Marc0-dev/SJ413-clock/CarClock/src/PCF8563.c

#include "PCF8563.h"
void Write(uint8_t reg, unsigned char value){
    IIC_Init(400000, WRITE_ADDRESS);
    while( I2C_GetFlagStatus(I2C1, I2C_FLAG_BUSY) != RESET);
    I2C_GenerateSTART(I2C1, ENABLE);
    while( !I2C_CheckEvent( I2C1, I2C_EVENT_MASTER_MODE_SELECT ) );
    I2C_Send7bitAddress( I2C1, WRITE_ADDRESS, I2C_Direction_Transmitter );
    while (!I2C_CheckEvent(I2C1, I2C_EVENT_MASTER_TRANSMITTER_MODE_SELECTED));
    while (I2C_GetFlagStatus(I2C1, I2C_FLAG_TXE) == RESET);
    I2C_SendData(I2C1, reg);
    while (!I2C_CheckEvent(I2C1, I2C_EVENT_MASTER_BYTE_TRANSMITTED));
    I2C_SendData(I2C1, value);
    while (!I2C_CheckEvent(I2C1, I2C_EVENT_MASTER_BYTE_TRANSMITTED));
    I2C_GenerateSTOP(I2C1, ENABLE);
}
unsigned char Read(uint8_t reg){
    IIC_Init(400000, READ_ADDRESS);
    while( I2C_GetFlagStatus(I2C1, I2C_FLAG_BUSY) != RESET);
    I2C_GenerateSTART(I2C1, ENABLE);
    while( !I2C_CheckEvent( I2C1, I2C_EVENT_MASTER_MODE_SELECT ) );
    I2C_Send7bitAddress( I2C1, READ_ADDRESS, I2C_Direction_Transmitter );
    while (!I2C_CheckEvent(I2C1, I2C_EVENT_MASTER_TRANSMITTER_MODE_SELECTED));
    while (I2C_GetFlagStatus(I2C1, I2C_FLAG_TXE) == RESET);
    I2C_SendData(I2C1, reg);
    while (!I2C_CheckEvent(I2C1, I2C_EVENT_MASTER_BYTE_TRANSMITTED));
    I2C_GenerateSTOP(I2C1, ENABLE);
    IIC_Init(400000, READ_ADDRESS);
    while( I2C_GetFlagStatus(I2C1, I2C_FLAG_BUSY) != RESET);
    I2C_GenerateSTART(I2C1, ENABLE);
    while( !I2C_CheckEvent( I2C1, I2C_EVENT_MASTER_MODE_SELECT ) );
    I2C_Send7bitAddress( I2C1, READ_ADDRESS, I2C_Direction_Receiver );
    while (!I2C_CheckEvent(I2C1, I2C_EVENT_MASTER_RECEIVER_MODE_SELECTED));
    unsigned char data = I2C_ReceiveData(I2C1);
    while (!I2C_CheckEvent(I2C1, I2C_EVENT_MASTER_BYTE_RECEIVED));
    I2C_GenerateSTOP(I2C1, ENABLE);
    return data;
}
void QueryTime(unsigned char  * min, unsigned char * hour){
    IIC_Init(400000, READ_ADDRESS);
    while( I2C_GetFlagStatus(I2C1, I2C_FLAG_BUSY) != RESET);
    I2C_GenerateSTART(I2C1, ENABLE);
    while( !I2C_CheckEvent( I2C1, I2C_EVENT_MASTER_MODE_SELECT ) );
    I2C_Send7bitAddress( I2C1, READ_ADDRESS, I2C_Direction_Transmitter );
    while (!I2C_CheckEvent(I2C1, I2C_EVENT_MASTER_TRANSMITTER_MODE_SELECTED));
    while (I2C_GetFlagStatus(I2C1, I2C_FLAG_TXE) == RESET);
    I2C_SendData(I2C1, 0x02);
    while (!I2C_CheckEvent(I2C1, I2C_EVENT_MASTER_BYTE_TRANSMITTED));
    I2C_GenerateSTOP(I2C1, ENABLE);
    IIC_Init(400000, READ_ADDRESS);
    while( I2C_GetFlagStatus(I2C1, I2C_FLAG_BUSY) != RESET);
    I2C_GenerateSTART(I2C1, ENABLE);
    while( !I2C_CheckEvent( I2C1, I2C_EVENT_MASTER_MODE_SELECT ) );
    I2C_Send7bitAddress( I2C1, READ_ADDRESS, I2C_Direction_Receiver );
    while (!I2C_CheckEvent(I2C1, I2C_EVENT_MASTER_RECEIVER_MODE_SELECTED));
    while (I2C_GetFlagStatus(I2C1, I2C_FLAG_RXNE) == RESET);
    I2C_ReceiveData(I2C1);
    while (!I2C_CheckEvent(I2C1, I2C_EVENT_MASTER_BYTE_RECEIVED));
    *min = I2C_ReceiveData(I2C1);
    while (!I2C_CheckEvent(I2C1, I2C_EVENT_MASTER_BYTE_RECEIVED));
    *hour = I2C_ReceiveData(I2C1);
    while (!I2C_CheckEvent(I2C1, I2C_EVENT_MASTER_BYTE_RECEIVED));
    I2C_GenerateSTOP(I2C1, ENABLE);
}
void WriteTime(unsigned char * min, unsigned char * hour){
    IIC_Init(400000, WRITE_ADDRESS);
    while( I2C_GetFlagStatus(I2C1, I2C_FLAG_BUSY) != RESET);
    I2C_GenerateSTART(I2C1, ENABLE);
    while( !I2C_CheckEvent( I2C1, I2C_EVENT_MASTER_MODE_SELECT ) );
    I2C_Send7bitAddress( I2C1, WRITE_ADDRESS, I2C_Direction_Transmitter );
    while (!I2C_CheckEvent(I2C1, I2C_EVENT_MASTER_TRANSMITTER_MODE_SELECTED));
    while (I2C_GetFlagStatus(I2C1, I2C_FLAG_TXE) == RESET);
    I2C_SendData(I2C1, 0x02);
    while (!I2C_CheckEvent(I2C1, I2C_EVENT_MASTER_BYTE_TRANSMITTED));
    I2C_SendData(I2C1, 0x00);
    while (!I2C_CheckEvent(I2C1, I2C_EVENT_MASTER_BYTE_TRANSMITTED));
    I2C_SendData(I2C1, *min);
    while (!I2C_CheckEvent(I2C1, I2C_EVENT_MASTER_BYTE_TRANSMITTED));
    I2C_SendData(I2C1, *hour);
    I2C_GenerateSTOP(I2C1, ENABLE);
}
