Marc0-dev/SJ413-clock/CarClock/src/BoardInit.c

#include "BoardInit.h"
void init(){
    NVIC_PriorityGroupConfig(NVIC_PriorityGroup_1);
    SystemCoreClockUpdate();
    Delay_Init();
    USART_Printf_Init(115200);
}
void initPin(uint8_t pinNumber, char bank, uint8_t mode, uint8_t speed){
    GPIO_InitTypeDef GPIO_InitStructure = {0};
    GPIO_InitStructure.GPIO_Pin = pinNumber;
    GPIO_InitStructure.GPIO_Mode = mode;
    GPIO_InitStructure.GPIO_Speed = speed;
    if(bank == 'A'){
        RCC_APB2PeriphClockCmd(RCC_APB2Periph_GPIOA, ENABLE);
        GPIO_Init(GPIOA, &GPIO_InitStructure);
    }
    else if(bank == 'C'){
        RCC_APB2PeriphClockCmd(RCC_APB2Periph_GPIOC, ENABLE);
        GPIO_Init(GPIOC, &GPIO_InitStructure);
    }
    else if(bank == 'D'){
        RCC_APB2PeriphClockCmd(RCC_APB2Periph_GPIOD, ENABLE);
        GPIO_Init(GPIOD, &GPIO_InitStructure);
    }
}
void IIC_Init(u32 speed, u16 address){
    I2C_InitTypeDef I2C_InitStructure = {0};
    GPIO_InitTypeDef GPIO_InitStructure={0};
    RCC_APB2PeriphClockCmd(RCC_APB2Periph_GPIOC | RCC_APB2Periph_AFIO, ENABLE);
    RCC_APB1PeriphClockCmd(RCC_APB1Periph_I2C1, ENABLE);
    GPIO_InitStructure.GPIO_Pin = GPIO_Pin_2;
    GPIO_InitStructure.GPIO_Mode = GPIO_Mode_AF_OD;
    GPIO_InitStructure.GPIO_Speed = GPIO_Speed_50MHz;
    GPIO_Init( GPIOC, &GPIO_InitStructure );
    GPIO_InitStructure.GPIO_Pin = GPIO_Pin_1;
    GPIO_InitStructure.GPIO_Mode = GPIO_Mode_AF_OD;
    GPIO_InitStructure.GPIO_Speed = GPIO_Speed_50MHz;
    GPIO_Init( GPIOC, &GPIO_InitStructure );
    I2C_InitStructure.I2C_ClockSpeed = speed;
    I2C_InitStructure.I2C_Mode = I2C_Mode_I2C;
    I2C_InitStructure.I2C_DutyCycle = I2C_DutyCycle_2;
    I2C_InitStructure.I2C_OwnAddress1 = address;
    I2C_InitStructure.I2C_Ack = I2C_Ack_Enable;
    I2C_InitStructure.I2C_AcknowledgedAddress = I2C_AcknowledgedAddress_7bit;
    I2C_Init(I2C1, &I2C_InitStructure);
    I2C_Cmd(I2C1, ENABLE);
    I2C_AcknowledgeConfig(I2C1, ENABLE);
}
